brendena/pebble_steel_flex_cable/images/back1Removed.png

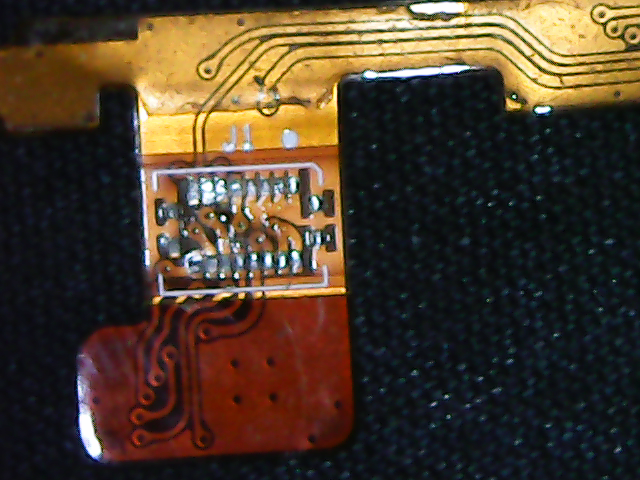
images/back1Removed.png
