brendena/pebble_steel_flex_cable/images/back5.png

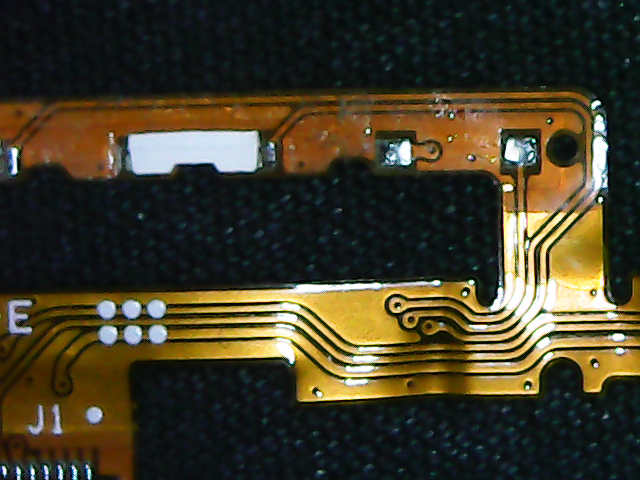
images/back5.png
