brendena/pebble_steel_flex_cable/images/back6Removed.png

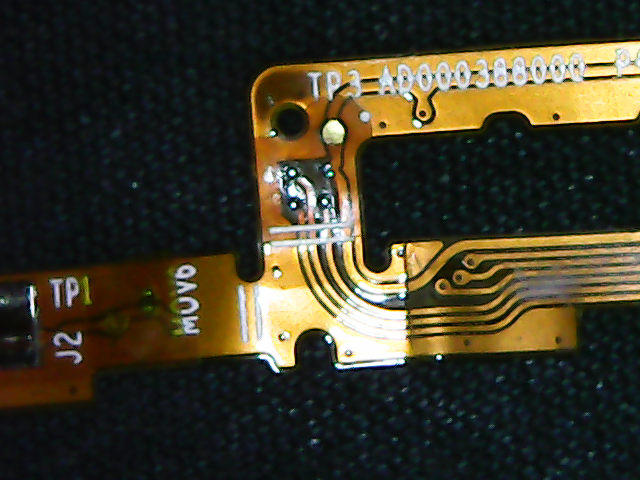
images/back6Removed.png
