brendena/pebble_steel_flex_cable/images/FlatBedScanBack.jpg

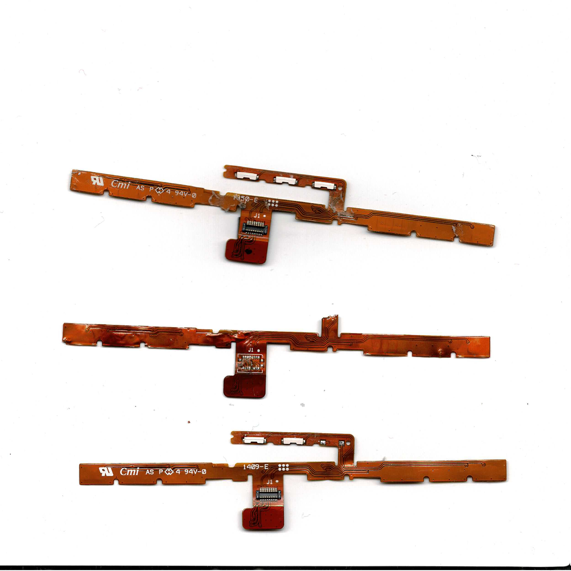
images/FlatBedScanBack.jpg
