brendena/pebble_steel_flex_cable/images/front1Removed.png

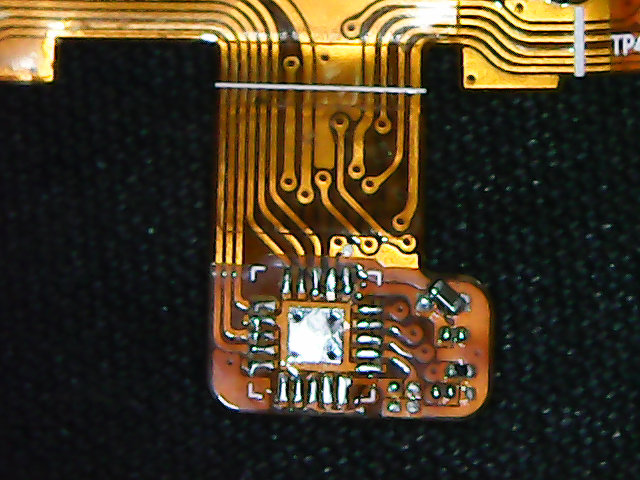
images/front1Removed.png
