brendena/pebble_steel_flex_cable/images/front2.png

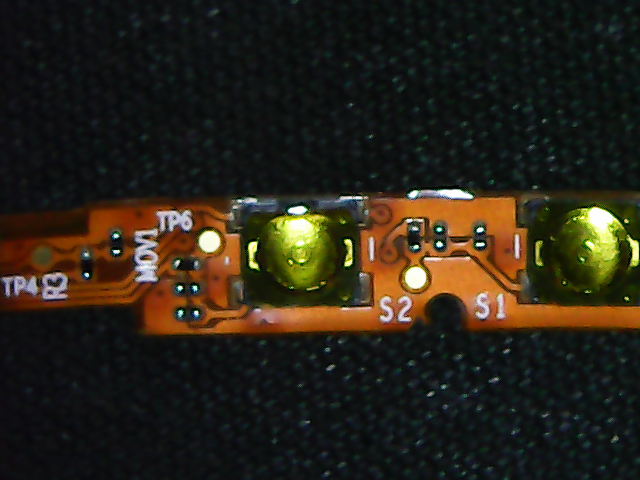
images/front2.png
