brendena/pebble_steel_flex_cable/images/front2Removed.png

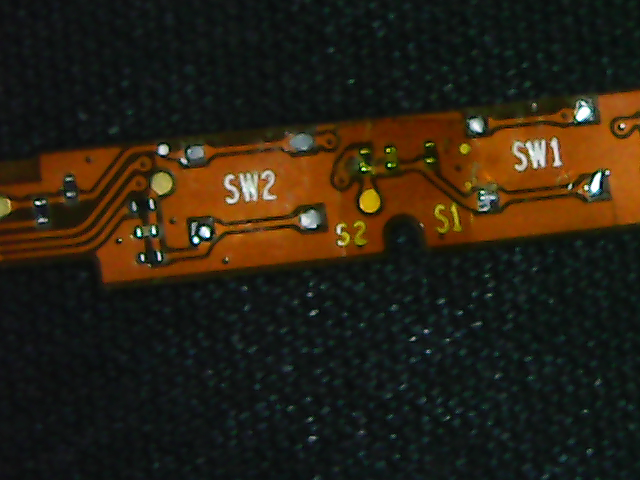
images/front2Removed.png
